SamyFrancelet/PongBoy/0000_Docs/0009_Misc/GroveConnector.PNG

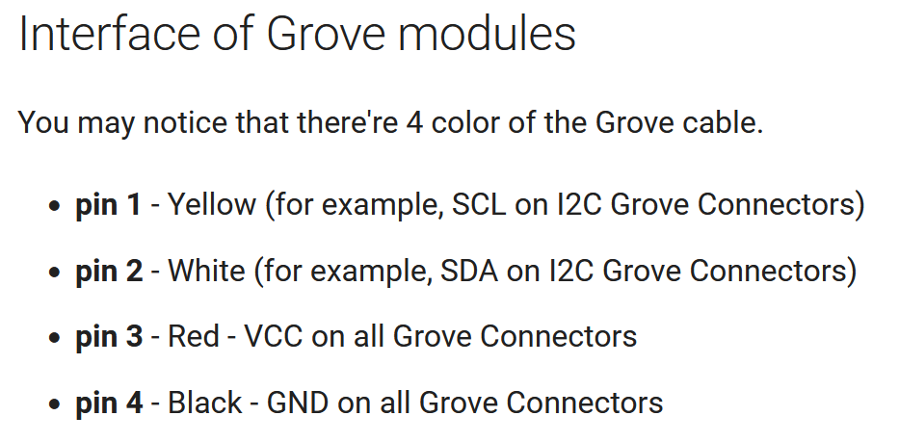
0000_Docs/0009_Misc/GroveConnector.PNG
