SamyFrancelet/PongBoy/0200_Research/0202_Simulations/Reverse_polarity_protection/NMOS_protection.asc

M1: nmos; Si9436DY
R1: res; 100k
Rload: res; 1k
V1: voltage; 3V
Named nets: 0
.tran 1s
