SamyFrancelet/PongBoy/0500_Firmware/PongBoy.X/src/globaldefs.h

/* 
 * File:   globaldefs.h
 * Author: samy
 *
 * Created on 3. septembre 2021, 09:45
 */

#ifndef GLOBALDEFS_H
#define	GLOBALDEFS_H

#define TICKINTERVAL 10
#define _XTAL_FREQ 64000000

#endif	/* GLOBALDEFS_H */
